DeWeElectronics/PIO_F401_Keyboard/src/GPIO_Config.c

/*!
 * @file GPIO_Config.c
 * @author Demitrias Wilbert
 * @brief definition of each pin configuration structure type (PinId_t)
 * @version 0.1
 * @date 2021-07-08
 * 
 * 
*/

#include "GPIO_Config.h"

#ifdef GPIOA
const PinId_t PIN_PA0 = {GPIOA, (1 << 0), 0};
const PinId_t PIN_PA1 = {GPIOA, (1 << 1), 1};
const PinId_t PIN_PA2 = {GPIOA, (1 << 2), 2};
const PinId_t PIN_PA3 = {GPIOA, (1 << 3), 3};
const PinId_t PIN_PA4 = {GPIOA, (1 << 4), 4};
const PinId_t PIN_PA5 = {GPIOA, (1 << 5), 5};
const PinId_t PIN_PA6 = {GPIOA, (1 << 6), 6};
const PinId_t PIN_PA7 = {GPIOA, (1 << 7), 7};
const PinId_t PIN_PA8 = {GPIOA, (1 << 8), 8};
const PinId_t PIN_PA9 = {GPIOA, (1 << 9), 9};
const PinId_t PIN_PA10 = {GPIOA, (1 << 10), 10};
const PinId_t PIN_PA11 = {GPIOA, (1 << 11), 11};
const PinId_t PIN_PA12 = {GPIOA, (1 << 12), 12};
const PinId_t PIN_PA13 = {GPIOA, (1 << 13), 13};
const PinId_t PIN_PA14 = {GPIOA, (1 << 14), 14};
const PinId_t PIN_PA15 = {GPIOA, (1 << 15), 15};
#endif // GPIOA

#ifdef GPIOB
const PinId_t PIN_PB0 = {GPIOB, (1 << 0), 0};
const PinId_t PIN_PB1 = {GPIOB, (1 << 1), 1};
const PinId_t PIN_PB2 = {GPIOB, (1 << 2), 2};
const PinId_t PIN_PB3 = {GPIOB, (1 << 3), 3};
const PinId_t PIN_PB4 = {GPIOB, (1 << 4), 4};
const PinId_t PIN_PB5 = {GPIOB, (1 << 5), 5};
const PinId_t PIN_PB6 = {GPIOB, (1 << 6), 6};
const PinId_t PIN_PB7 = {GPIOB, (1 << 7), 7};
const PinId_t PIN_PB8 = {GPIOB, (1 << 8), 8};
const PinId_t PIN_PB9 = {GPIOB, (1 << 9), 9};
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
const PinId_t PIN_PK11 = {GPIOK, (1 << 11), 11};
const PinId_t PIN_PK12 = {GPIOK, (1 << 12), 12};
const PinId_t PIN_PK13 = {GPIOK, (1 << 13), 13};
const PinId_t PIN_PK14 = {GPIOK, (1 << 14), 14};
const PinId_t PIN_PK15 = {GPIOK, (1 << 15), 15};
#endif // GPIOK
